SantoshDasari-ai/In-Vitro-Pulsatile-Flow-Thrombogenicity-Tester/CAD/complete SJM valve 2.SLDASM

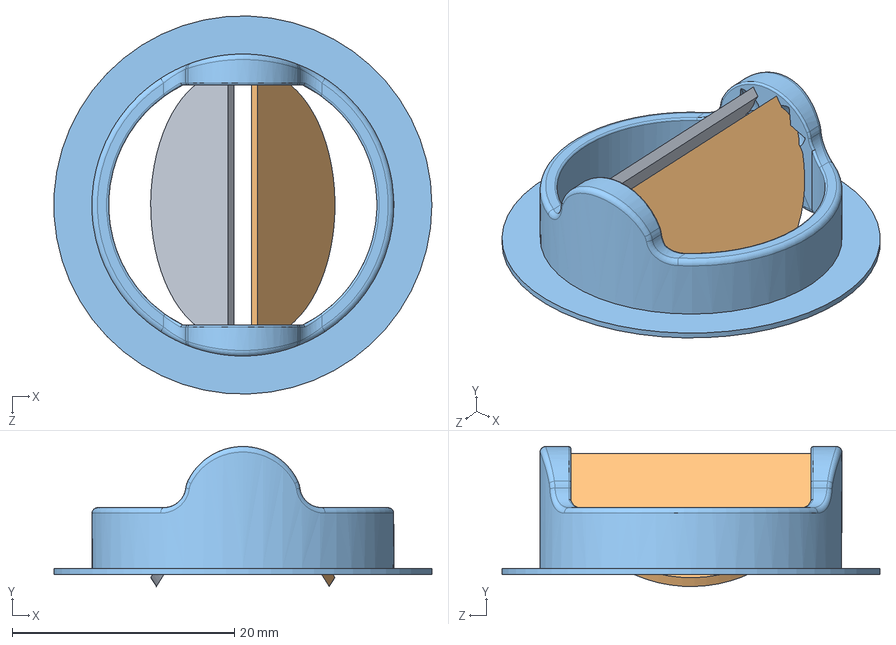
[picture p2: CAD file, 2025-05-24]
CAD/complete SJM valve 2.SLDASM
34.0 x 12.6 x 34.0 mm
Single Block with Hinges
leaflet
Mirrorleaflet2
