SantoshDasari-ai/In-Vitro-Pulsatile-Flow-Thrombogenicity-Tester/CAD/Mirrorleaflet2.SLDPRT

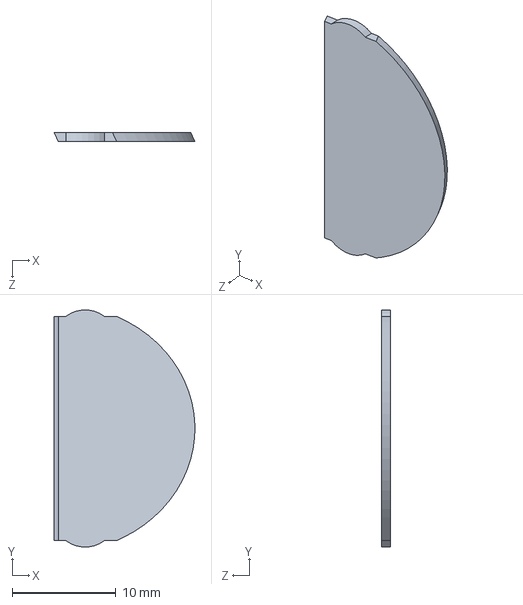
[picture p16: CAD file, 2025-05-24]
CAD/Mirrorleaflet2.SLDPRT
13.6 x 22.8 x 0.864 mm
