SantoshDasari-ai/In-Vitro-Pulsatile-Flow-Thrombogenicity-Tester/CAD/DM860I_TGT_Motor_Driver.SLDPRT

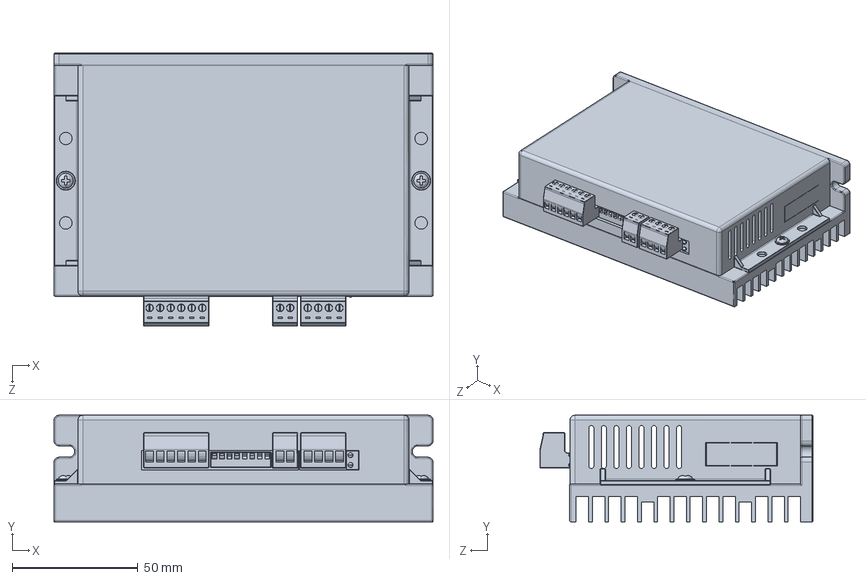
[picture p17: CAD file, 2025-05-24]
CAD/DM860I_TGT_Motor_Driver.SLDPRT
151.0 x 42.5 x 108.9 mm
