SantoshDasari-ai/In-Vitro-Pulsatile-Flow-Thrombogenicity-Tester/CAD/Round Half Tube.SLDPRT

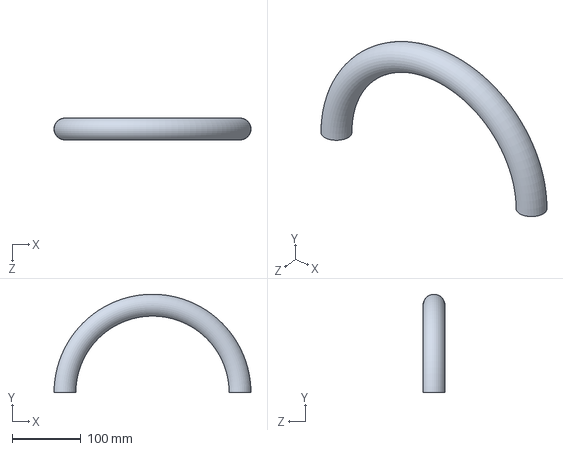
[picture p18: CAD file, 2025-05-24]
CAD/Round Half Tube.SLDPRT
285.8 x 142.9 x 31.8 mm
