SantoshDasari-ai/In-Vitro-Pulsatile-Flow-Thrombogenicity-Tester/CAD/End Cap.SLDPRT

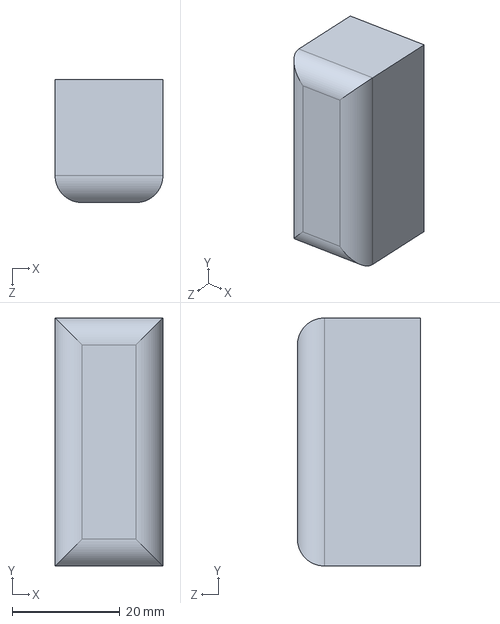
[picture p19: CAD file, 2025-05-24]
CAD/End Cap.SLDPRT
20.0 x 46.0 x 22.9 mm
