SantoshDasari-ai/In-Vitro-Pulsatile-Flow-Thrombogenicity-Tester/CAD/ST-M7_TGT_Motor_Bracket.SLDPRT

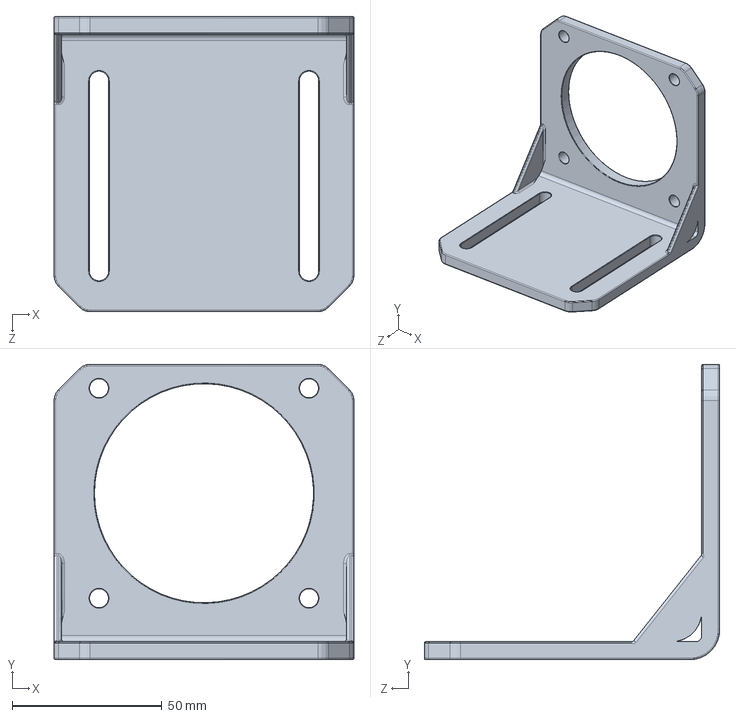
[picture p20: CAD file, 2025-05-24]
CAD/ST-M7_TGT_Motor_Bracket.SLDPRT
100.0 x 98.5 x 98.5 mm
