SantoshDasari-ai/In-Vitro-Pulsatile-Flow-Thrombogenicity-Tester/CAD/Round Blood-Loop Assembly.SLDASM

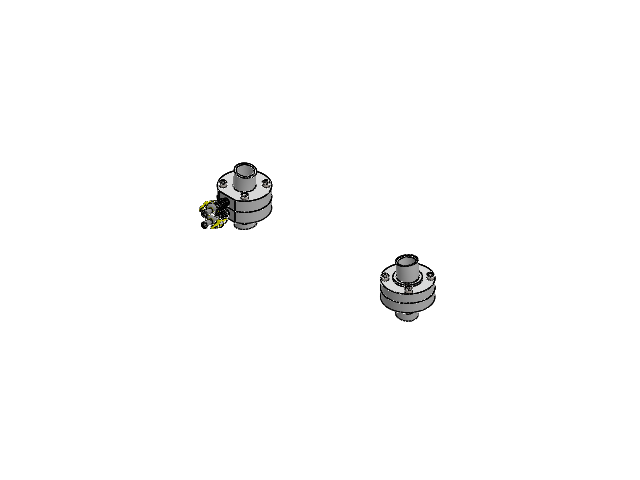
[picture p22: CAD file, 2025-05-24]
CAD/Round Blood-Loop Assembly.SLDASM
Round Half Tube x 2
SJM Fill Port x 2
1163N125_Clean Room Viton Fluoroelastomer O-Ring
hex nut jam_am x 8
51525K223_Plastic Quick-Turn Tube Coupling x 2
socket head cap screw_am x 8
SJM Valve Housing x 2
1163N126_Clean Room Viton Fluoroelastomer O-Ring
Single Block with Hinges
leaflet
Mirrorleaflet2
7033T24_On-Off Valve for Water, Oil, and Inert Gas x 2
