SantoshDasari-ai/In-Vitro-Pulsatile-Flow-Thrombogenicity-Tester/CAD/Motor_and_Bracket_SubAssem.SLDASM

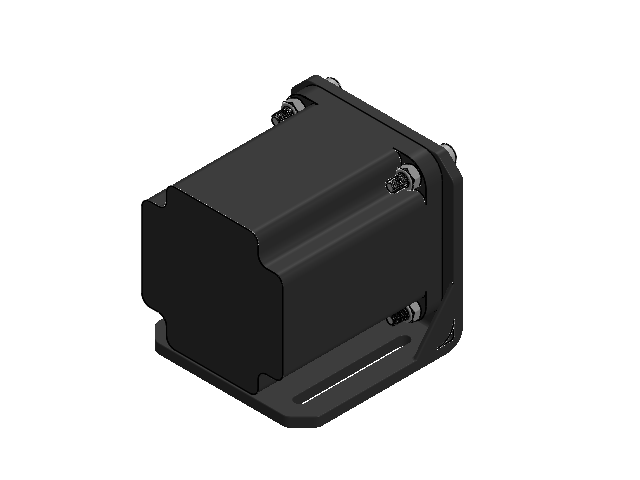
[picture p23: CAD file, 2025-05-24]
CAD/Motor_and_Bracket_SubAssem.SLDASM
ST-M7_TGT_Motor_Bracket
34HS38-5204S_TGT_Motor
91292A139_18-8 Stainless Steel Socket Head Screw x 4
93625A250_18-8 Stainless Steel Nylon-Insert Locknut x 4
