SantoshDasari-ai/In-Vitro-Pulsatile-Flow-Thrombogenicity-Tester/CAD/Fill Port Subassembly.SLDASM

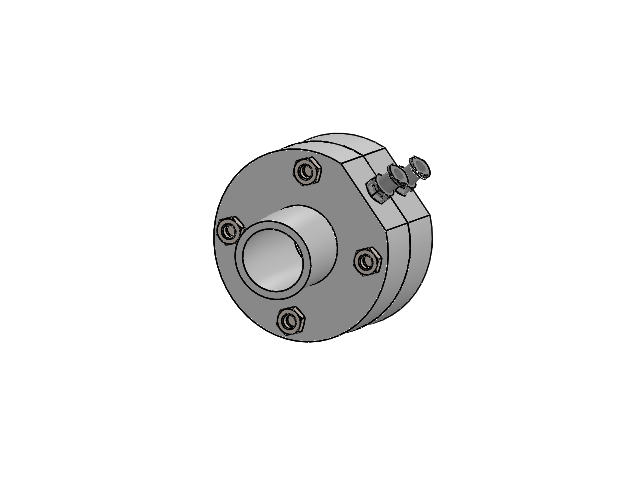
[picture p24: CAD file, 2025-05-24]
CAD/Fill Port Subassembly.SLDASM
SJM Fill Port x 2
1163N125_Clean Room Viton Fluoroelastomer O-Ring
hex nut jam_am x 4
51525K223_Plastic Quick-Turn Tube Coupling x 2
socket head cap screw_am x 4
